hipe-0/RotaryJoystick/20230826_142422.jpg

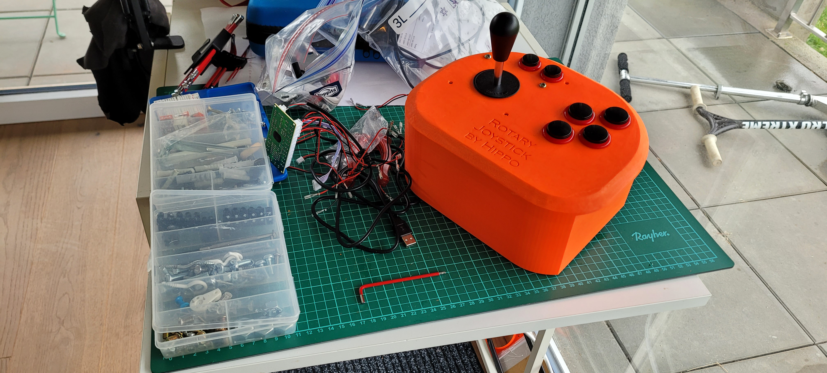
20230826_142422.jpg
