hipe-0/RotaryJoystick/20230826_161948.jpg

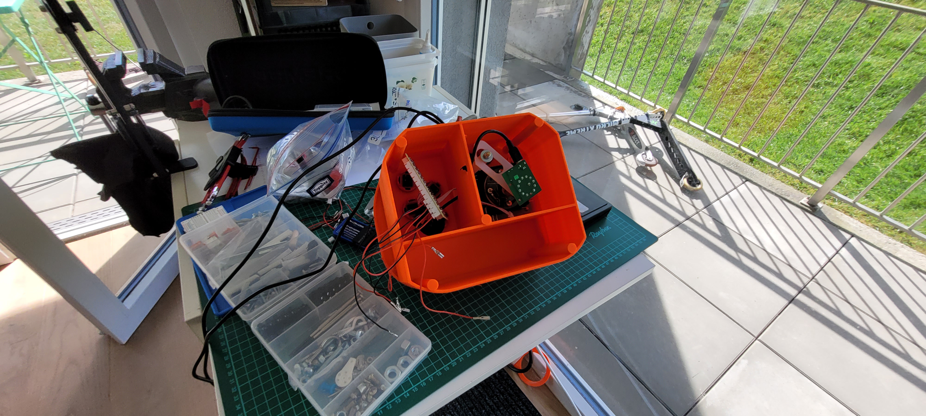
20230826_161948.jpg
