hipe-0/RotaryJoystick/20230829_080209.jpg

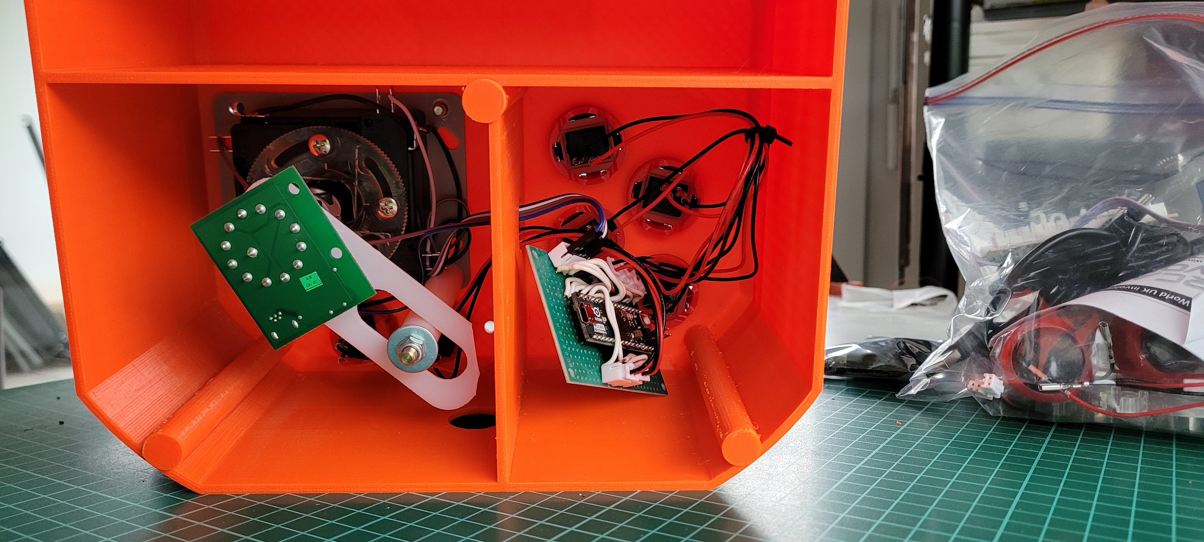
20230829_080209.jpg
