hipe-0/RotaryJoystick/20230911_161405.jpg

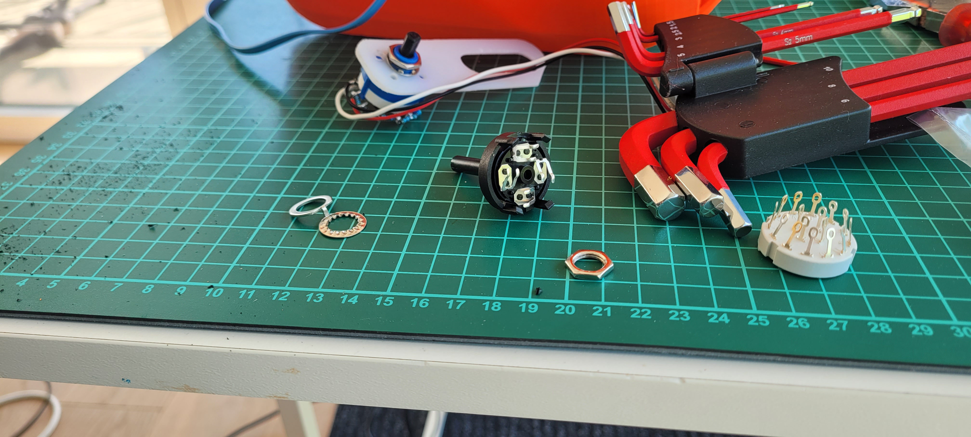
20230911_161405.jpg
