hipe-0/RotaryJoystick/20231220_153523.jpg

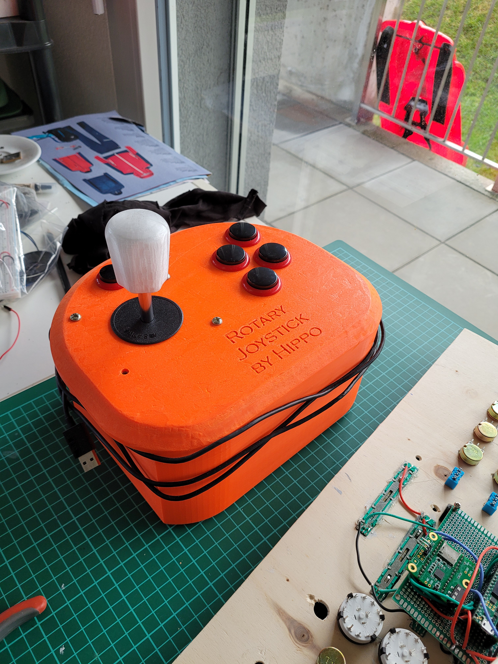
20231220_153523.jpg
